polihedron/Weight-scale/software/STM32F411_ILI9341_HX711/TouchGFX/gui/include/gui/common/NumericKeyboardLayout.hpp

#ifndef NUMERIC_KEYBOARD_LAYOUT
#define NUMERIC_KEYBOARD_LAYOUT

#include <touchgfx/widgets/Keyboard.hpp>
#include <touchgfx/hal/Types.hpp>
#include <fonts/ApplicationFontProvider.hpp>
#include "BitmapDatabase.hpp"

using namespace touchgfx;

static const int SPACE_Y_BETWEEN_KEYS_NUMERIC = 4;

static const int KEY_WIDTH_NUMERIC  = 39;
static const int KEY_HEIGHT_NUMERIC = 53;

static const int KEY_ROW_1_Y_NUMERIC = 64;
static const int KEY_ROW_2_Y_NUMERIC = KEY_ROW_1_Y_NUMERIC + SPACE_Y_BETWEEN_KEYS_NUMERIC + KEY_HEIGHT_NUMERIC;
static const int KEY_ROW_3_Y_NUMERIC = KEY_ROW_2_Y_NUMERIC + SPACE_Y_BETWEEN_KEYS_NUMERIC + KEY_HEIGHT_NUMERIC;
static const int KEY_ROW_4_Y_NUMERIC = KEY_ROW_3_Y_NUMERIC + SPACE_Y_BETWEEN_KEYS_NUMERIC + KEY_HEIGHT_NUMERIC;

static const int KEY_ROW_1_X_NUMERIC = 7;
static const int KEY_ROW_1_X_KEY_DISTANCE_NUMERIC = 40;

static const int KEY_ROW_2_X_NUMERIC = KEY_ROW_1_X_NUMERIC;
static const int KEY_ROW_2_X_KEY_DISTANCE_NUMERIC = KEY_ROW_1_X_KEY_DISTANCE_NUMERIC;

static const int KEY_ROW_3_X_NUMERIC = KEY_ROW_1_X_NUMERIC;
static const int KEY_ROW_3_X_KEY_DISTANCE_NUMERIC = KEY_ROW_1_X_KEY_DISTANCE_NUMERIC;

static const int KEY_ROW_4_X_NUMERIC = KEY_ROW_1_X_NUMERIC;
static const int KEY_ROW_4_X_KEY_DISTANCE_NUMERIC = KEY_ROW_1_X_KEY_DISTANCE_NUMERIC;

static const int BACKSPACE_X_NUMERIC = KEY_ROW_2_X_NUMERIC + KEY_ROW_1_X_KEY_DISTANCE_NUMERIC * 3;
static const int EXIT_X_NUMERIC = KEY_ROW_4_X_NUMERIC + KEY_ROW_1_X_KEY_DISTANCE_NUMERIC*4;
static const int OK_X_NUMERIC = KEY_ROW_3_X_NUMERIC + KEY_ROW_1_X_KEY_DISTANCE_NUMERIC*3;


/**
 * Array specifying the keys used in the CustomKeyboard.
 */
static const Keyboard::Key keyArrayNumeric[10] =
{
    { 1, Rect(KEY_ROW_1_X_NUMERIC                                       ,                 	KEY_ROW_1_Y_NUMERIC,	KEY_WIDTH_NUMERIC, 			KEY_HEIGHT_NUMERIC), BITMAP_KEYBOARD_KEY_HIGHLIGHTED_ID},
    { 2, Rect(KEY_ROW_1_X_NUMERIC + KEY_ROW_1_X_KEY_DISTANCE_NUMERIC    ,      				KEY_ROW_1_Y_NUMERIC, 	KEY_WIDTH_NUMERIC, 			KEY_HEIGHT_NUMERIC), BITMAP_KEYBOARD_KEY_HIGHLIGHTED_ID},
    { 3, Rect(KEY_ROW_1_X_NUMERIC + KEY_ROW_1_X_KEY_DISTANCE_NUMERIC * 2,  					KEY_ROW_1_Y_NUMERIC, 	KEY_WIDTH_NUMERIC, 			KEY_HEIGHT_NUMERIC), BITMAP_KEYBOARD_KEY_HIGHLIGHTED_ID},
    { 4, Rect(KEY_ROW_2_X_NUMERIC										,					KEY_ROW_2_Y_NUMERIC,	KEY_WIDTH_NUMERIC, 			KEY_HEIGHT_NUMERIC), BITMAP_KEYBOARD_KEY_HIGHLIGHTED_ID},
    { 5, Rect(KEY_ROW_2_X_NUMERIC + KEY_ROW_2_X_KEY_DISTANCE_NUMERIC    ,	   				KEY_ROW_2_Y_NUMERIC, 	KEY_WIDTH_NUMERIC, 			KEY_HEIGHT_NUMERIC), BITMAP_KEYBOARD_KEY_HIGHLIGHTED_ID},
    { 6, Rect(KEY_ROW_2_X_NUMERIC + KEY_ROW_2_X_KEY_DISTANCE_NUMERIC * 2,   				KEY_ROW_2_Y_NUMERIC,	KEY_WIDTH_NUMERIC, 			KEY_HEIGHT_NUMERIC), BITMAP_KEYBOARD_KEY_HIGHLIGHTED_ID},
    { 7, Rect(KEY_ROW_3_X_NUMERIC 										,  					KEY_ROW_3_Y_NUMERIC,	KEY_WIDTH_NUMERIC, 			KEY_HEIGHT_NUMERIC), BITMAP_KEYBOARD_KEY_HIGHLIGHTED_ID},
    { 8, Rect(KEY_ROW_2_X_NUMERIC + KEY_ROW_3_X_KEY_DISTANCE_NUMERIC    , 					KEY_ROW_3_Y_NUMERIC,	KEY_WIDTH_NUMERIC, 			KEY_HEIGHT_NUMERIC), BITMAP_KEYBOARD_KEY_HIGHLIGHTED_ID},
    { 9, Rect(KEY_ROW_3_X_NUMERIC + KEY_ROW_3_X_KEY_DISTANCE_NUMERIC * 2, 					KEY_ROW_3_Y_NUMERIC, 	KEY_WIDTH_NUMERIC,			KEY_HEIGHT_NUMERIC), BITMAP_KEYBOARD_KEY_HIGHLIGHTED_ID},
    {10, Rect(KEY_ROW_3_X_NUMERIC + KEY_ROW_3_X_KEY_DISTANCE_NUMERIC * 3,  					KEY_ROW_3_Y_NUMERIC, 	KEY_WIDTH_NUMERIC,			KEY_HEIGHT_NUMERIC), BITMAP_KEYBOARD_KEY_HIGHLIGHTED_ID},
};

/**
 * Callback areas for the special buttons on the CustomKeyboard.
 */
 static Keyboard::CallbackArea callbackAreasNumeric[3] =
{
    {Rect(BACKSPACE_X_NUMERIC,  KEY_ROW_2_Y_NUMERIC,KEY_WIDTH_NUMERIC*2 , KEY_HEIGHT_NUMERIC), 0, BITMAP_KEYBOARD_KEY_DELETE_HIGHLIGHTED_ID },   // backspace

    {Rect(EXIT_X_NUMERIC,  KEY_ROW_3_Y_NUMERIC,KEY_WIDTH_NUMERIC , KEY_HEIGHT_NUMERIC), 0, BITMAP_KEYBOARD_KEY_EXIT_HIGHLIGHTED_ID },   // backspace

    {Rect(OK_X_NUMERIC,  KEY_ROW_1_Y_NUMERIC,KEY_WIDTH_NUMERIC*2 , KEY_HEIGHT_NUMERIC), 0, BITMAP_KEYBOARD_KEY_OK_HIGHLIGHTED_ID }   // backspace
};

/**
 * The layout for the CustomKeyboard.
 */
static const Keyboard::Layout layoutNumeric =
{
    BITMAP_KEYBOARD_BACKGROUND_ID,
    keyArrayNumeric,
	10,
    callbackAreasNumeric,
    3,
    Rect(0, 5, 200, 50),
    TypedText(T_ENTEREDTEXT),
#if !defined(USE_BPP) || USE_BPP==16
    0xFFFFFF,
#elif USE_BPP==24
	0xFFFFFF,
#elif USE_BPP==4
    0xF,
#elif USE_BPP==2
    0xF,
#else
#error Unknown USE_BPP
#endif
    Typography::KEYBOARDNUMERIC,
#if !defined(USE_BPP) || USE_BPP==16
	0,
#elif USE_BPP==24
	0,
#endif
};

#endif
